willdickson/pupae_thermal_device/firmware/pupae_thermal_device/constants.h

#ifndef CONSTANTS_H
#define CONSTANTS_H
#include <Arduino.h>

extern const uint32_t SERIAL_BAUDRATE;
extern const uint32_t LOOP_DT;

constexpr uint32_t NUM_CONTROLLER = 2;
extern const uint8_t SENSOR_ADDRESS[NUM_CONTROLLER]; 
extern const uint8_t DRIVE_MOTOR_NUMBER[NUM_CONTROLLER];

#endif
