willdickson/pupae_thermal_device/software/pupae-thermal-device/src/pupae_thermal_device/constants.py

PLOT_TEMPERATURE_MAX = 38.0
PLOT_TEMPERATURE_MIN = 14.0
PLOT_TEMPERATURE_MID = 0.5*(PLOT_TEMPERATURE_MIN + PLOT_TEMPERATURE_MAX)

PLOT_POWER_MAX =  5000.0
PLOT_POWER_MIN = -5000.0

#PLOT_POWER_MAX =  120.0
#PLOT_POWER_MIN = -120.0
